jalal-shahini/jMacro/bottom_layer.png

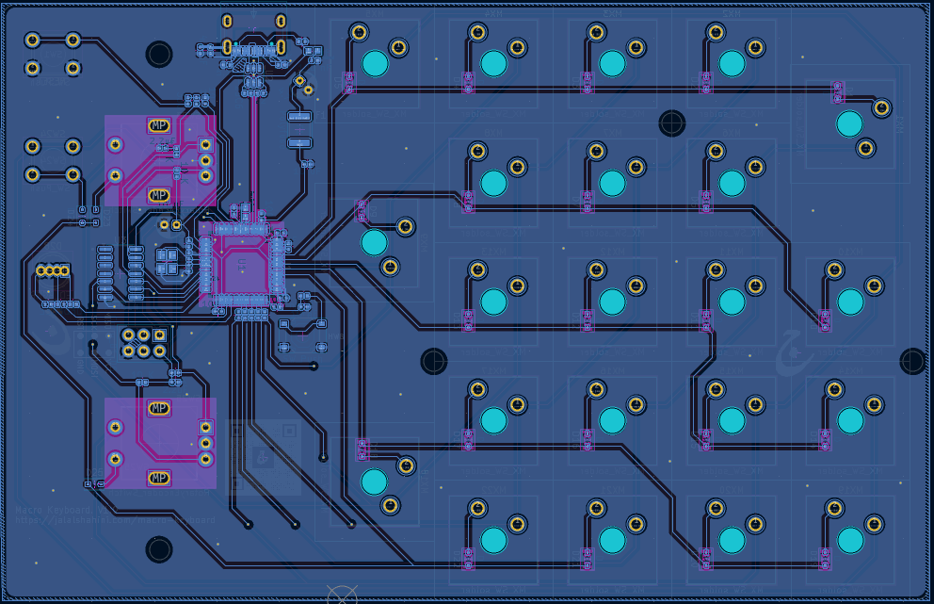
bottom_layer.png
